kuwatay/6502ctrl/hardware/rev2/6502ctrl-mega2-schematic.png

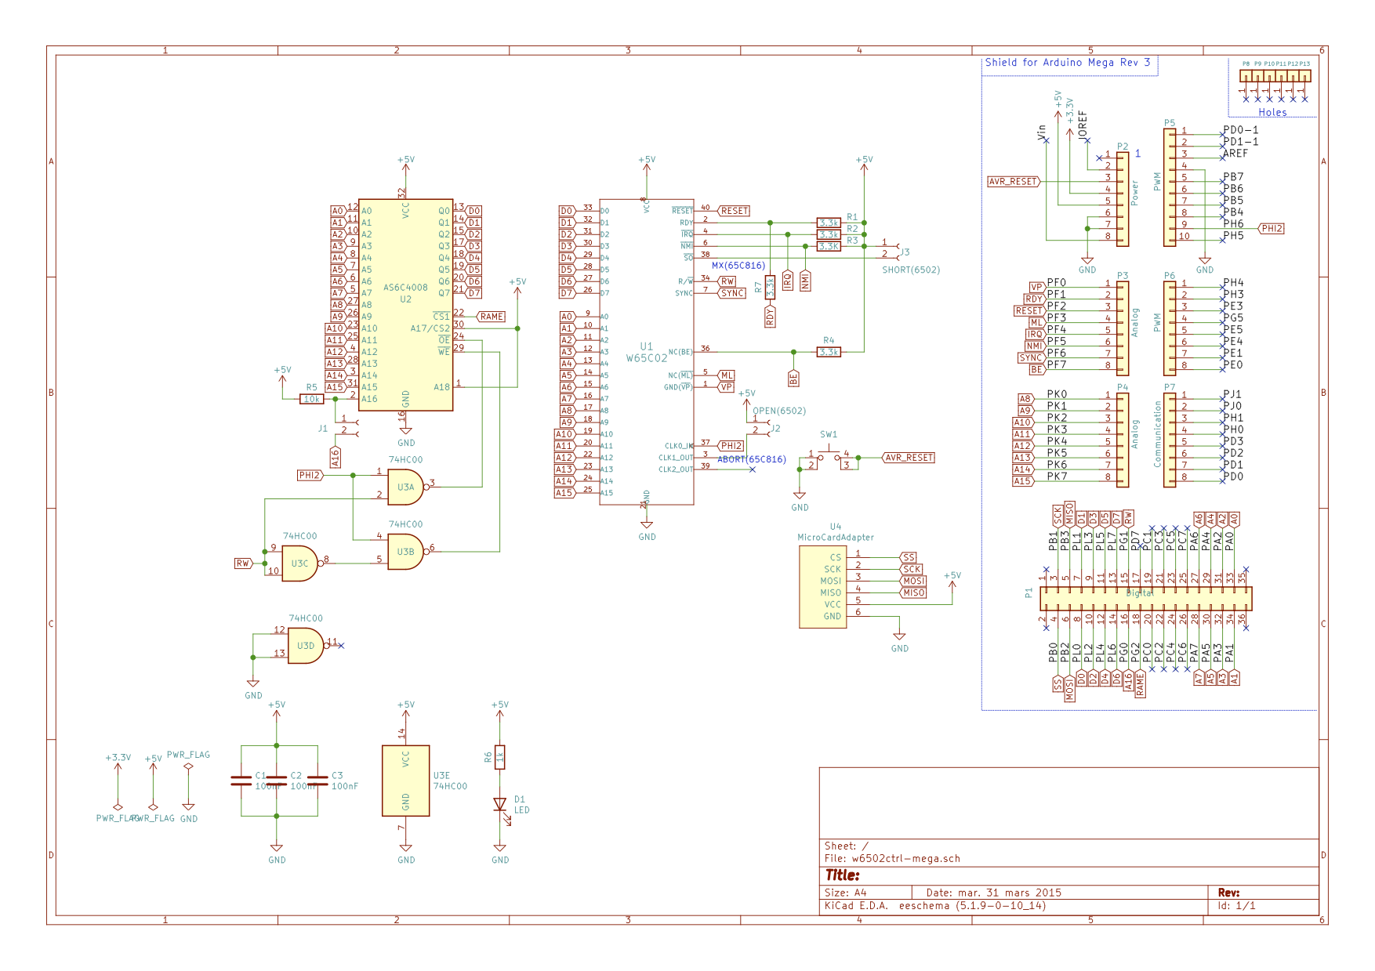
hardware/rev2/6502ctrl-mega2-schematic.png
